tedfernau/WWUWINDFEED/firmware/html/images/sailboat.jpeg

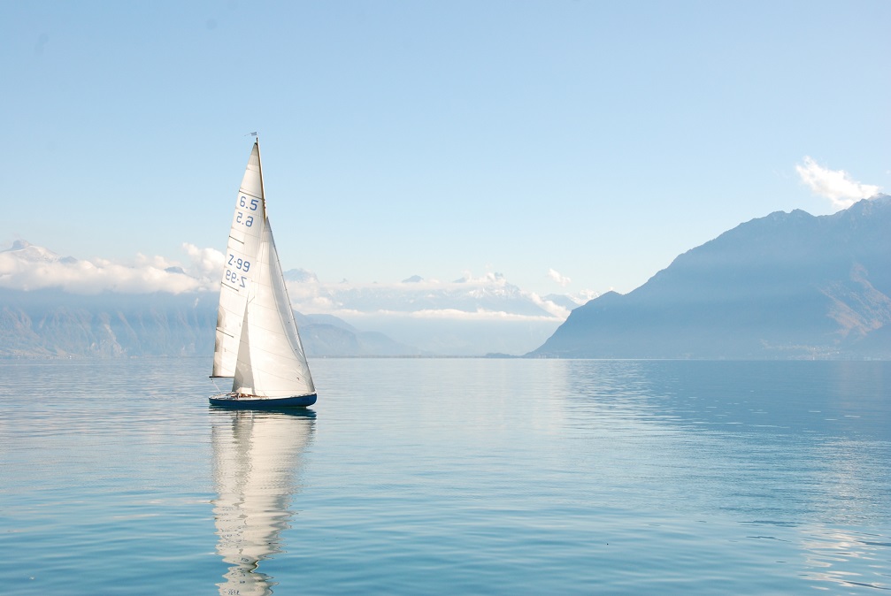
firmware/html/images/sailboat.jpeg
