tedfernau/WWUWINDFEED/images/3-Afterreflow.jpg

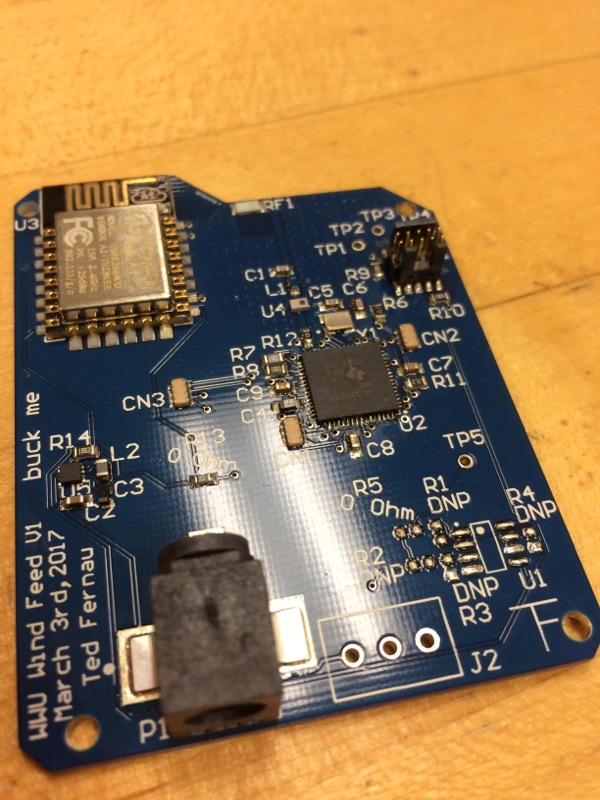
images/3-Afterreflow.jpg
