tedfernau/WWUWINDFEED/images/4-Cleaning traces under microscope.JPG

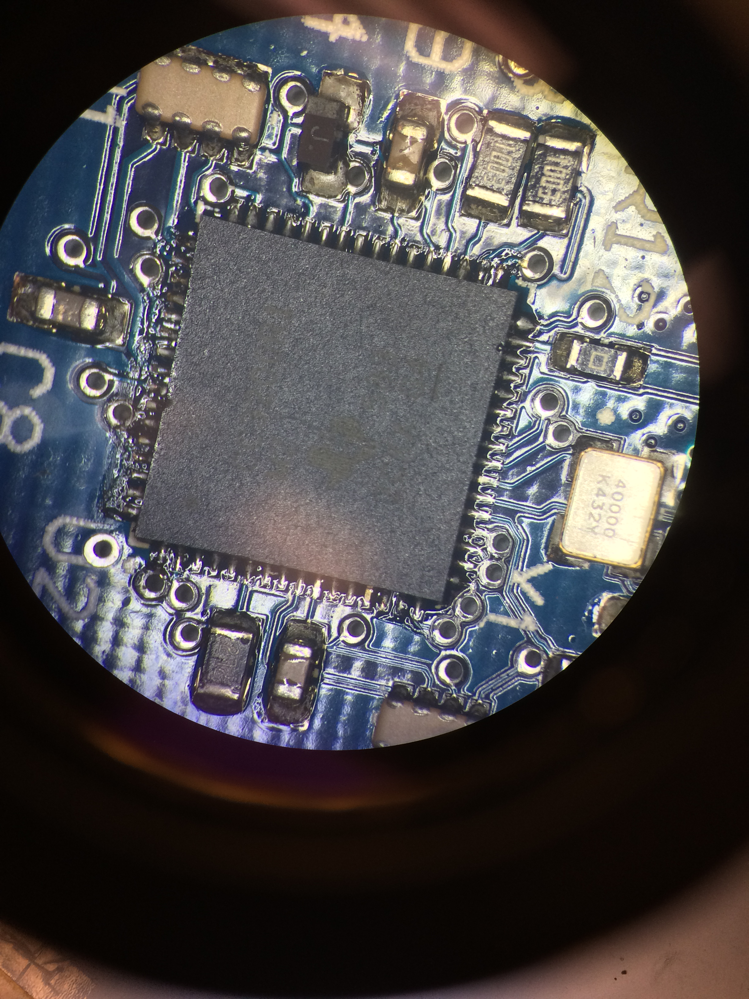
images/4-Cleaning traces under microscope.JPG
