tedfernau/WWUWINDFEED/images/5-V5.jpg

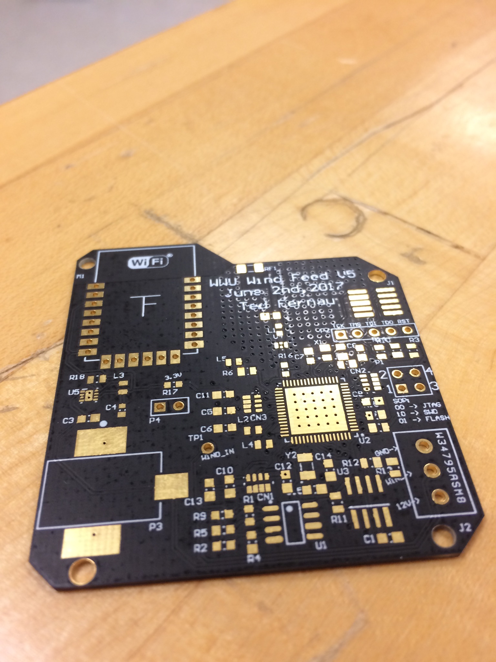
images/5-V5.jpg
